EI2030/Archer/firmware/ec/source/debug_usb.h

/*
 * debug_usb.h
 *
 *  Created on: May 18, 2021
 *      Author: wenting
 */

#ifndef DEBUG_USB_H_
#define DEBUG_USB_H_

#include "virtual_com.h"

/*******************************************************************************
 * Definitions
 ******************************************************************************/
#if defined(USB_DEVICE_CONFIG_EHCI) && (USB_DEVICE_CONFIG_EHCI > 0)
#define CONTROLLER_ID kUSB_ControllerEhci0
#endif
#if defined(USB_DEVICE_CONFIG_KHCI) && (USB_DEVICE_CONFIG_KHCI > 0)
#define CONTROLLER_ID kUSB_ControllerKhci0
#endif
#if defined(USB_DEVICE_CONFIG_LPCIP3511FS) && (USB_DEVICE_CONFIG_LPCIP3511FS > 0U)
#define CONTROLLER_ID kUSB_ControllerLpcIp3511Fs0
#endif
#if defined(USB_DEVICE_CONFIG_LPCIP3511HS) && (USB_DEVICE_CONFIG_LPCIP3511HS > 0U)
#define CONTROLLER_ID kUSB_ControllerLpcIp3511Hs0
#endif

#define USB_DEVICE_INTERRUPT_PRIORITY (3U)
typedef struct _usb_device_composite_struct
{
    usb_device_handle deviceHandle;                           /* USB device handle. */
    usb_cdc_vcom_struct_t cdcVcom[USB_DEVICE_CONFIG_CDC_ACM]; /* CDC virtual com device structure. */
    uint8_t speed;  /* Speed of USB device. USB_SPEED_FULL/USB_SPEED_LOW/USB_SPEED_HIGH.                 */
    uint8_t attach; /* A flag to indicate whether a usb device is attached. 1: attached, 0: not attached */
    uint8_t currentConfiguration; /* Current configuration value. */
    uint8_t
        currentInterfaceAlternateSetting[USB_INTERFACE_COUNT]; /* Current alternate setting value for each interface. */
} usb_device_composite_struct_t;

/*******************************************************************************
 * API
 ******************************************************************************/
/*!
 * @brief CDC class specific callback function.
 *
 * This function handles the CDC class specific requests.
 *
 * @param handle          The CDC ACM class handle.
 * @param event           The CDC ACM class event type.
 * @param param           The parameter of the class specific request.
 *
 * @return A USB error code or kStatus_USB_Success.
 */
extern usb_status_t USB_DeviceCdcVcomCallback(class_handle_t handle, uint32_t event, void *param);

/*!
 * @brief Virtual COM device set configuration function.
 *
 * This function sets configuration for CDC class.
 *
 * @param handle The CDC ACM class handle.
 * @param configure The CDC ACM class configure index.
 *
 * @return A USB error code or kStatus_USB_Success.
 */
extern usb_status_t USB_DeviceCdcVcomSetConfigure(class_handle_t handle, uint8_t configure);
/*!
 * @brief Virtual COM device initialization function.
 *
 * This function initializes the device with the composite device class information.
 *
 * @param deviceComposite The pointer to the composite device structure.
 *
 * @return A USB error code or kStatus_USB_Success.
 */
extern usb_status_t USB_DeviceCdcVcomInit(usb_device_composite_struct_t *deviceComposite);
/*!
 * @brief Application task function.
 *
 * This function runs the task for application.
 *
 * @return None.
 */
extern void USB_DeviceCdcVcomTask(void);

#endif /* DEBUG_USB_H_ */
